eric-mjk/berry-good-bot/berry_perception/testCode/image.png

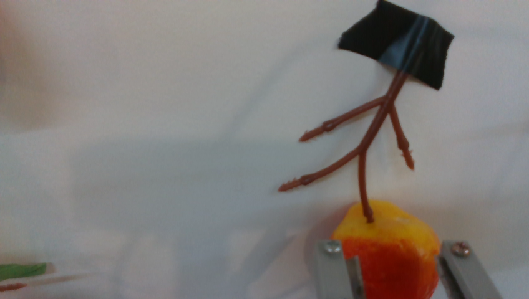
berry_perception/testCode/image.png
