eric-mjk/berry-good-bot/berry_perception/test/tmp/bottom_debug_1755084621.png

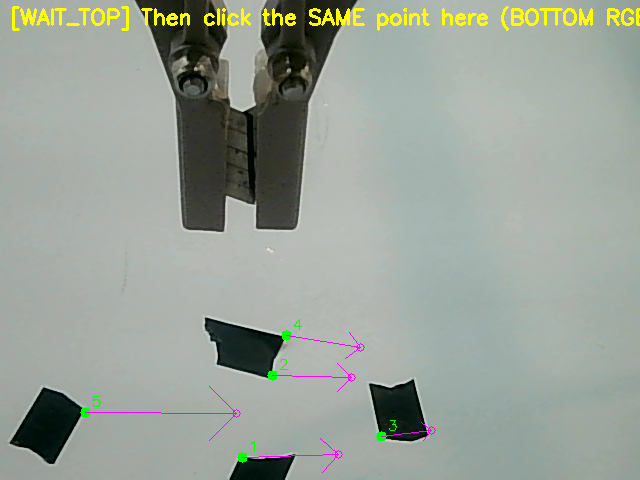
berry_perception/test/tmp/bottom_debug_1755084621.png
