eric-mjk/berry-good-bot/robot/sample_moveit_config/config/initial_positions.yaml

# Default initial positions for berry_good_bot's ros2_control fake system

initial_positions:
  gripper_joint: 0
  joint1: 0
  joint2: 0
  joint3: 0
  screw_joint: 0
  wrist_roll_joint: 0
